CarbixEnergy/Carbix-Energy-Monitor/Docs/pics/readmepic.jpg

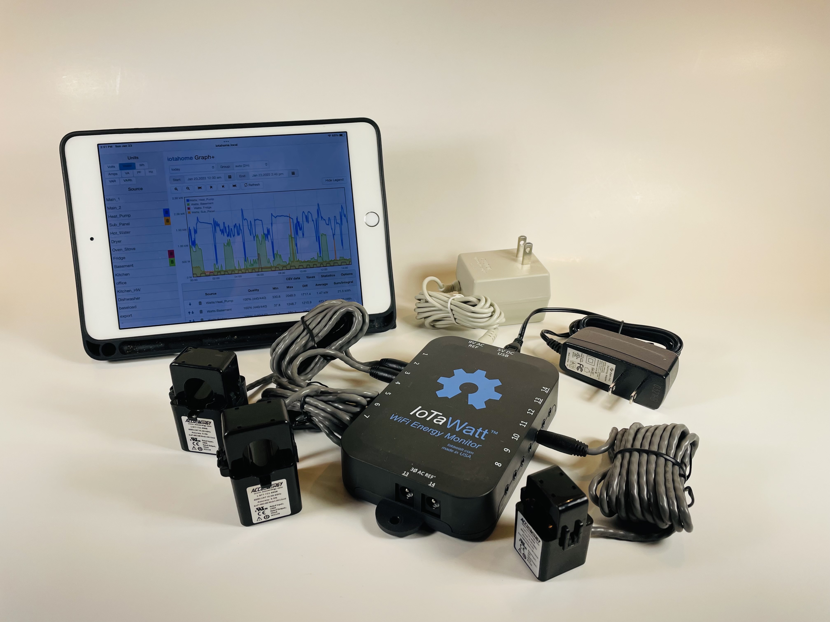
Docs/pics/readmepic.jpg
