CarbixEnergy/Carbix-Energy-Monitor/Docs/pics/USAbundle.jpg

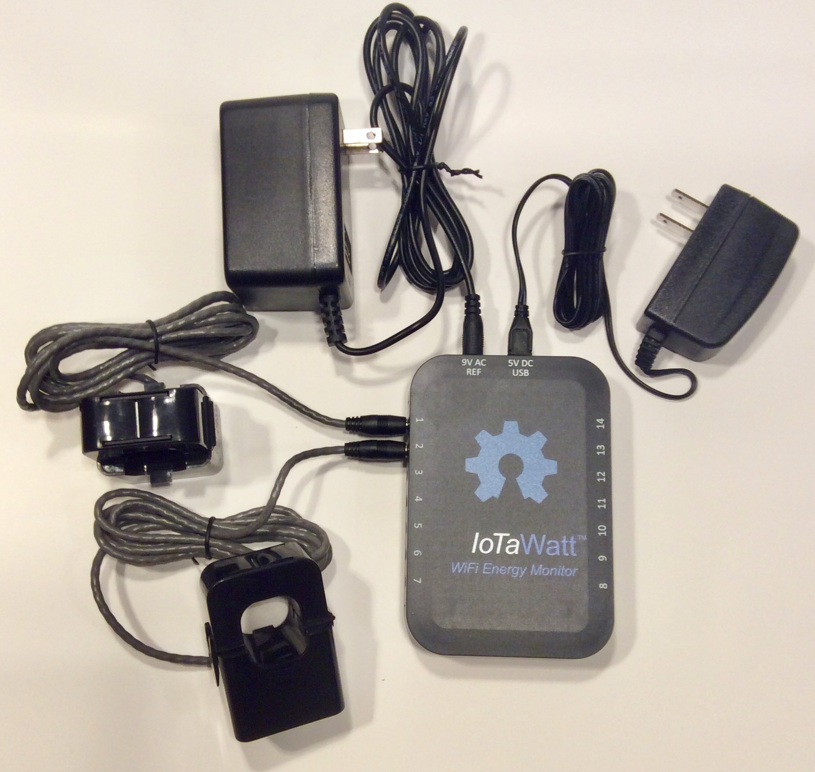
Docs/pics/USAbundle.jpg
