CarbixEnergy/Carbix-Energy-Monitor/Firmware/CarbixEnergyMonitor/updater.cpp

#include "CarbixEnergyMonitor.h"

bool   unpackUpdate(String updateVersion);

static const char updateURL_P[] PROGMEM = CARBIX_UPDATE_HOST;
static const char updatePath_P[] = CARBIX_VERSIONS_PATH;

/*************************************************************************************************
 * 
 *          updater - Service to check and update firmware
 * 
 *************************************************************************************************/
uint32_t updater(struct serviceBlock* _serviceBlock) {
  enum states {initialize, checkAutoUpdate, getVersion, waitVersion, createFile, download, waitDownload, install, getTable, waitTable};
  static states state = initialize;
  static asyncHTTPrequest* request = nullptr;
  static String updateVersion;
  static File releaseFile;
  static bool upToDate = false;
  static bool parseError = false;
  static int checkResponse = 0;
  static char* _updateClass = nullptr;
  static uint32_t lastVersionCheck = 0;
  static long latestTableVersion = -1;
  static uint32_t HTTPtoken = 0;

  trace(T_UPDATE,0); 
  if( ! WiFi.isConnected()){
    return UTCtime() + 1;
  }

  switch(state){

    case initialize: {
      trace(T_UPDATE,1);
      if( ! updateClass){
        updateClass = charstar("NONE");
      } 
      log("Updater: service started. Auto-update class is %s", updateClass);
      _updateClass = charstar(updateClass);
      tableVersion = getTablesVersion();
      state = checkAutoUpdate;
      return 1;
    }

    case checkAutoUpdate: {
      trace(T_UPDATE,2); 
      if( ! updateClass){
        updateClass = charstar("NONE");
      }
      if(strcmp(updateClass, _updateClass) != 0){
        delete[] _updateClass;
        _updateClass = charstar(updateClass);
        log("Updater: Auto-update class changed to %s", _updateClass);
        if (strcmp(updateClass, "NONE") != 0){
          lastVersionCheck = 0;
          upToDate = false;
          state = getVersion;
          return 1;
        }
      }
      else if (strcmp(_updateClass, "NONE") != 0 && UTCtime() - lastVersionCheck > updaterServiceInterval){
        lastVersionCheck = UTCtime();
        state = getVersion;
        return 1;
      }
      return UTCtime() + 7;
    }

    case getVersion: {
      trace(T_UPDATE,3); 
      if( ! WiFi.isConnected()){
        return UTCtime() + 1;
      }
      HTTPtoken = HTTPreserve(T_UPDATE);
      if( ! HTTPtoken){
        return UTCtime() + 1;
      }
      if( ! request){
        request = new asyncHTTPrequest;
      }
      request->setDebug(false);
      String URL(FPSTR(updateURL_P));
      URL += FPSTR(updatePath_P);
      if( ! request->open("GET", URL.c_str())){
        HTTPrelease(HTTPtoken);
        return UTCtime() + 60;
      }
      request->setTimeout(10);
      if( ! request->send()){
        request->abort();
        HTTPrelease(HTTPtoken);;
        return UTCtime() + 60;
      }
      state = waitVersion;
      return 1;
    }

    case waitVersion: {
      trace(T_UPDATE,4); 
      if(request->readyState() != 4){
        return UTCtime() + 1;
      }
      HTTPrelease(HTTPtoken);
      int responseCode = request->responseHTTPcode();
      String responseText = request->responseText();
      delete request;
      request = nullptr;

          // Handle error response

      if(responseCode != 200){
        if( responseCode != checkResponse){
          log("Updater: Invalid response from server. HTTPcode: %d", responseCode);
        }
        checkResponse = responseCode;
        state = checkAutoUpdate;
        if(responseCode == 403){
          lastVersionCheck = UTCtime();
        }
        return UTCtime() + 301;
      }
      DynamicJsonBuffer Json;
      JsonObject& response = Json.parseObject(responseText);
      if( ! response.success()){
        if(!parseError){
          log("Updater: could not parse versions.json file.");
        }
        parseError = true;
        state = checkAutoUpdate;
        lastVersionCheck = UTCtime();
        return 1;
      }
      parseError = false;

      // Check for "classes" object

      JsonObject& classes = response[F("classes")];
      if( ! classes.success()){
        if(!parseError){
          log("Updater: versions.json is invalid.");
        }
        parseError = true;
        state = checkAutoUpdate;
        lastVersionCheck = UTCtime();
        return 1;
      }      

            // Check if response contains the configured auto-update class

      if(classes.containsKey(updateClass)){
        updateVersion = classes[updateClass].as<char*>();
        if(updateVersion.equals(CARBIX_ENERGY_MONITOR_VERSION)){
          if( ! upToDate){
            log("Updater: Auto-update is current for class %s.", updateClass);
            upToDate = true;
          }
        }
        else {
          log("Updater: Update from %s to %s", CARBIX_ENERGY_MONITOR_VERSION, updateVersion.c_str());
          state = createFile;
          return 1;
        }
      }
      else {
        log("Updater: Unrecognized auto-update class %s.", updateClass);
        upToDate = true;
      }

            // Check tables file version

      if(response.containsKey(F("tables"))){
        latestTableVersion = parseSemanticVersion(response[F("tables")].as<char *>());
        if (latestTableVersion > tableVersion){
          log("Updater: update tables from %s to %s", displaySemanticVersion(tableVersion).c_str(), displaySemanticVersion(latestTableVersion).c_str());
          state = getTable;
          return 1;
        }
      }

      state = checkAutoUpdate;
      lastVersionCheck = UTCtime();
      return 1;
    }

    case createFile: {
      trace(T_UPDATE,5); 
      log("Updater: download %s", updateVersion.c_str());
      String filePath = "download/" + updateVersion + ".bin";
      deleteRecursive(filePath);
      releaseFile = SD.open(filePath.c_str(), FILE_WRITE);
      if(! releaseFile){
        log("Updater: Cannot create download file.");
        state = checkAutoUpdate;
        return UTCtime() + 60;
      }
      state = download;
      return 1;
    }
      
    case download: {
      trace(T_UPDATE,6);   
      if( ! WiFi.isConnected()){
        return UTCtime() + 1;
      }
      HTTPtoken = HTTPreserve(T_UPDATE, true);
      if( ! HTTPtoken){
        return UTCtime() + 1;
      }
      if( ! request){
        request = new asyncHTTPrequest;
      }
      String URL = String(FPSTR(updateURL_P)) + String(F(CARBIX_VERSIONS_DIR)) + updateVersion + ".bin";
      request->setDebug(false);
      trace(T_UPDATE,6);   
      if( ! request->open("GET", URL.c_str())){
        log("Updater: Cannot GET %s.", URL.c_str());
        HTTPrelease(HTTPtoken);
        state = checkAutoUpdate;
        lastVersionCheck = UTCtime();
        return 1;
      }
      trace(T_UPDATE,6);   
      request->setTimeout(5);
      request->onData([](void* arg, asyncHTTPrequest* request, size_t available){
        uint8_t *buf = new uint8_t[500];
        while(request->available()){
          size_t read = request->responseRead(buf, 500);
          releaseFile.write(buf, read);
        }
        delete[] buf;
        });
      request->send();

          // Writing to the SD in async handler can cause problems. If we return
          // and keep sampling, the onData handler could interupt another service
          // in the middle of SDcard work.  So we will go synchronous here and wait
          // for the entire update blob to be transfered and written to SD.
          // Takes about 5-10 seconds.

      setLedCycle(LED_UPDATING);
      while(request->readyState() != 4){
        yield();
      }
      trace(T_UPDATE,6);   
      endLedCycle();
      HTTPrelease(HTTPtoken);
      size_t fileSize = releaseFile.size();
      releaseFile.close();
      trace(T_UPDATE,6);   
      if(request->responseHTTPcode() != 200){
        log("Updater: Download failed HTTPcode %d", request->responseHTTPcode());
        delete request;
        request = nullptr;
        String filePath = "download/" + updateVersion + ".bin";
        deleteRecursive(filePath);
        state = checkAutoUpdate;
        lastVersionCheck = UTCtime();
        return 1;
      }
      log("Updater: Release downloaded %dms, size %d", request->elapsedTime(), fileSize);
      releaseFile.close();
      delete request;
      request = nullptr;
      state = install;
      return 1;
    }

    case install: {
      trace(T_UPDATE,7); 
      if(unpackUpdate(updateVersion)){
        if(installUpdate(updateVersion)){
          log ("Updater: Firmware updated, restarting.");
          delay(500);
          ESP.restart();
        }
      }
      state = checkAutoUpdate;
    }

    case getTable: {
      trace(T_UPDATE,10); 
      if( ! WiFi.isConnected()){
        return UTCtime() + 1;
      }
      HTTPtoken = HTTPreserve(T_UPDATE);
      if( ! HTTPtoken){
        return 250;
      }
      if( ! request){
        request = new asyncHTTPrequest;
      }
      String URL(FPSTR(CARBIX_UPDATE_HOST));
      URL += F(CARBIX_TABLE_DIR);
      URL += displaySemanticVersion(latestTableVersion);
      URL += ".txt";
      request->setDebug(false);
      if( ! request->open("GET", URL.c_str())){
        HTTPrelease(HTTPtoken);
        return UTCtime() + 60;
      }
      request->setTimeout(10);
      if( ! request->send()){
        request->abort();
        HTTPrelease(HTTPtoken);;
        return UTCtime() + 60;
      }
      state = waitTable;
      return 1;
    }

    case waitTable: {
      trace(T_UPDATE,20); 
      if(request->readyState() != 4){
        return 250;
      }
      HTTPrelease(HTTPtoken);
      int responseCode = request->responseHTTPcode();

          // Handle response

      if(responseCode == 200){
        if(SD.exists(F(CARBIX_NEW_TABLE_PATH))) SD.remove(F(CARBIX_NEW_TABLE_PATH));
        File tableFile = SD.open(F(CARBIX_NEW_TABLE_PATH), FILE_WRITE);
        if(!tableFile){
          return false;
        }
        uint8_t buf[512];
        while(request->available()){
          int len = request->responseRead(buf, 512);
          tableFile.write(buf, len);
        }
        tableFile.close();
        SD.remove(F(CARBIX_TABLE_PATH));
        SDFS.rename(F(CARBIX_NEW_TABLE_PATH), F(CARBIX_TABLE_PATH));
        tableVersion = getTablesVersion();
      }
      delete request;
      request = nullptr;
      lastVersionCheck = UTCtime();
      state = checkAutoUpdate;
      return 100;
    }
  }
  return UTCtime() + 1;
}

/**************************************************************************************************
 * bool unpackUpdate(String version)
 * 
 * unpack the release blob to create a directory of support files to be
 * installed during the next restart, as well as the firmware binary
 * file with md-5 appendage to be installed before restart.
 * 
 * After unpacking, the signature on the file is verified using the CarbixEnergyMonitor public key.
 * Only release files from CarbixEnergyMonitor.com can be verified because the private-key is needed to
 * sign with the digital signature.
 * 
 *************************************************************************************************/

bool unpackUpdate(String version){

  union {
    struct {
      char file[4];
      uint32_t len;
      char name[24];
    } fileHeader;
    struct { 
      char CarbixEnergyMonitor[8];
      char release[8];
    } updtHeader;
    uint8_t header[32];
  } headers;

  bool binaryFound = false;
  SHA256 sha256;
  MD5Builder md5;

        // open the release file and setup to sha256

  String filePath = "download/" + version + ".bin";
  File releaseFile = SD.open((char*)filePath.c_str(), FILE_READ);
  if(! releaseFile){
    log("Updater: %s not found", filePath.c_str());
    return false;
  }
  int signatureSize = 64;
  uint32_t binarySize = releaseFile.size() - signatureSize;
  sha256.reset();

        // Read and verify the header

  if(true){
    releaseFile.read(headers.header,sizeof(headers.updtHeader));
    sha256.update(headers.header,sizeof(headers.updtHeader));
    binarySize -= sizeof(headers.updtHeader);
    if((memcmp(headers.updtHeader.CarbixEnergyMonitor, "CarbixEM", 8) != 0) ||
       (memcmp(headers.updtHeader.release, version.c_str(), 8) != 0)) {
      log("Updater: release file header invalid. %s %s",headers.updtHeader.CarbixEnergyMonitor,headers.updtHeader.release);
      releaseFile.close();
      return false;
    }
  }
        // Create the local update directory.

  deleteRecursive(String(version));
  if( ! SD.mkdir(version.c_str())){
    log("Updater: Cannot create update directory");
    releaseFile.close();
    return false;
  }
        // Read the update blob and create the various files.

  while(binarySize){
    releaseFile.read(headers.header,sizeof(headers.fileHeader));
    sha256.update(headers.header,sizeof(headers.fileHeader));
    binarySize -= sizeof(headers.fileHeader);
    if(memcmp(headers.fileHeader.file,"FILE",4) != 0) {
      log("Updater: Release file format error.");
      releaseFile.close();
      return false;
    }
    String filename = String(headers.fileHeader.name);
    bool carbixenergymonitorBin = filename.equalsIgnoreCase("carbix.bin");
    if(carbixenergymonitorBin){
      binaryFound = true;
      md5.begin();
    }
    String filePath = version + "/" + headers.fileHeader.name;
    uint32_t fileSize = headers.fileHeader.len;
    File outFile = SD.open((char*)filePath.c_str(), FILE_WRITE);
    if( ! outFile){
      log("Updater: unable to create file: %s", filePath.c_str());
      releaseFile.close();
      return false;
    }
    int buffSize = 512;
    uint8_t* buff = new uint8_t [buffSize];
    while(fileSize){
      int chunk = MIN(fileSize, buffSize);
      if(chunk % 8) chunk += 8 - chunk % 8;
      releaseFile.read(buff, chunk);
      sha256.update(buff, chunk);
      binarySize -= chunk;
      outFile.write(buff, MIN(fileSize, buffSize));
      if(carbixenergymonitorBin) md5.add(buff, MIN(fileSize, buffSize));
      fileSize -= MIN(fileSize, buffSize);
    }
    delete[] buff;
    if(carbixenergymonitorBin) {
      md5.calculate();
      uint8_t md5Char[32];
      md5.getChars((char*)md5Char);
      outFile.write(md5Char, 32);
    }
    outFile.close();
    if(fileSize){
      return false;
    } 
  }
        // verify the signature

  
  uint8_t signature[64];
  uint8_t sha[32];
  sha256.finalize(sha,32);
  if(releaseFile.available() != 64){
    log("Updater: Update rejected, no signature.");
    releaseFile.close();
    return false;
  }
  releaseFile.read(signature, 64);
  releaseFile.close();
  
  uint8_t* key = new uint8_t[32];
  memcpy_P(key, publicKey, 32);
  if(! Ed25519::verify(signature, key, sha, 32)){
    log("Updater: Signature does not verify.");
    delete[] key;
    return false;
  }
  delete[] key;
  log("Updater: signature verified");
  return binaryFound;
}

/***********************************************************************************************************
 * bool installUpdate(String version)
 * 
 * Install the update in the directory "version".
 * Directory contains the ESP8266 binary "carbixenergymonitor.bin" with an md5 hash appended.
 * After binary is successfully updated, the ESP is restarted.
 * Upon restart, any files remaining in the update directory are 
 * placed in the SD root directory, replacing any pre-existing version.
 * 
 **********************************************************************************************************/

bool installUpdate(String version){
  UpdaterClass update;
  File inFile;
  String inPath = version + "/carbix.bin";
  inFile = SD.open((char*)inPath.c_str());
  if( ! inFile) return false;
  uint32_t inLen = inFile.size() - 32;
  update.begin(inLen);
  int buffSize = 512;
  uint8_t* buff = new uint8_t[buffSize];
  while(inLen){
    int chunk = MIN(inLen, buffSize);
    inFile.read(buff, chunk);
    update.write(buff, chunk);
    inLen -= chunk;
  }
  inFile.read(buff,32);
  update.setMD5((char*)buff);
  delete[] buff;
  if( ! update.end()){
    int error = update.getError();
    xbuf errorMsg;
    update.printError(errorMsg);
    log("Updater: %s", errorMsg.readStringUntil('\r').c_str());
    log("Updater: update failed");
    return false; 
  }
  SD.remove((char*)inPath.c_str());
  log("Updater: firmware upgraded to version %s", version.c_str());
  return true;
}

/************************************************************************************************************
 * bool copyUpdate(String version)
 * 
 * Copy release files staged in the update directory to the SD root.
 * Delete the files as they are copied and delete the directory when complete.
 * 
 ***********************************************************************************************************/

bool copyUpdate(String version){
  File updtDir = SD.open((char*)version.c_str());
  if( ! updtDir) return false;
  if( ! updtDir.isDirectory()){
    updtDir.close();
    SD.remove((char*)version.c_str());
    return false;
  }
  log("Updater: Installing update files for version %s", version.c_str());
  int buffSize = 512;
  uint8_t* buff = new uint8_t [buffSize];
  File inFile;
  while(inFile = updtDir.openNextFile()){
    if(strcmp_ci(inFile.name(),"config.txt") == 0 && SD.exists(inFile.name())){
      inFile.close();
      continue;
    }
    log("Updater: Installing %s", inFile.name());
    SD.remove(inFile.name());
    File outFile = SD.open(inFile.name(), FILE_WRITE);
    uint32_t fileSize = inFile.size();
    while(fileSize){
      int chunk = MIN(fileSize, buffSize);
      inFile.read(buff, chunk);
      outFile.write(buff, chunk);
      fileSize -= chunk;
    }
    inFile.close();
    outFile.close();
  }
  delete[] buff;
  log("Updater: Installation complete.");
  deleteRecursive(version);
  return true;
}

void printHex(uint8_t* data, size_t len){
  const char* hexchars = "0123456789abcdef";
  for(int i=0; i<len; i+=16){
    for(int j=i; j<(i+16); j++){
      if(j < len){
        Serial.print(hexchars[*data >> 4]);
        Serial.print(hexchars[*data++ & 0x0f]);
      }
      if((j % 4) == 3) Serial.print(" ");
    }
    Serial.println();
  }
}

long getTablesVersion(){
  File tableFile;
  tableFile = SD.open(F(CARBIX_TABLE_PATH), FILE_READ);
  if(!tableFile){
    return -1;
  }
  DynamicJsonBuffer Json;
  String tableSummary = JsonSummary(tableFile, 1);
  JsonObject& table = Json.parseObject(tableSummary);
  tableFile.close();

  if (!table.success()) {
    log("Table file parse failed.");
    return -1;
  }
  JsonObject &version = table[F("version")];
  if(table.containsKey(F("version"))){
    return parseSemanticVersion(table[F("version")].as<char*>());
  }
  return -1;
}
