CarbixEnergy/Carbix-Energy-Monitor/Firmware/CarbixEnergyMonitor/CSVquery.cpp

#include "CarbixEnergyMonitor.h"

CSVquery::CSVquery()
    :_oldRec(nullptr)
    ,_newRec(nullptr)
    ,_begin(0)
    ,_end(0)
    ,_limit(1000)
    ,_format(formatJson)
    ,_query(none)
    ,_header(false)
    ,_highRes(false)
    ,_integrations(false)
    ,_firstLine(true)
    ,_lastLine(false)
    ,_missingSkip(false)
    ,_missingNull(true)
    ,_missingZero(false)
    ,_timeOnly(false)
    ,_columns(nullptr)
    {}

CSVquery::~CSVquery(){
    trace(T_CSVquery,1,0);
    delete _oldRec;
    delete _newRec;
    trace(T_CSVquery,1,2);
    delete _columns;
    trace(T_CSVquery,1,3);
}

bool    CSVquery::setup(){
    trace(T_CSVquery,10);

                // query - show=series

    if(server.hasArg(F("show"))){
        String arg = server.arg(F("show"));
        if(arg.equalsIgnoreCase("series")){
           _format = formatJson;
           _query = show;
            return true; 
        }
        return false;
    }

                // query - select=[  ] 

    else if (server.hasArg(F("select"))){
    
        if( ! (server.hasArg(F("begin")) && server.hasArg(F("end")) && server.hasArg(F("group")) )){
            _failReason = F("Missing begin, end or group.");
            return false;
        }
       
        _begin = parseTimeArg(server.arg(F("begin")));
        if(_begin % Current_log.interval()){
            _begin += Current_log.interval() - (_begin % Current_log.interval());
        }
        _end = parseTimeArg(server.arg(F("end")));
        if(_end % Current_log.interval()){
            _end -= _end % Current_log.interval();
        }
        if(_end == 0 || _begin == 0 || _end < _begin) return false;
        trace(T_CSVquery,10);

        if(server.hasArg(F("resolution"))){
            String arg = server.arg(F("resolution"));
            if(arg.equalsIgnoreCase("low")){
                _highRes = false;
            }
            else if(arg.equalsIgnoreCase("high")){
                _highRes = true;
            }
            else {
                _failReason = F("Invalid resolution");
                return false;
            }
        }

        trace(T_CSVquery,10);
        String group = server.arg(F("group"));
        if(group.equals("auto")){
            const uint16_t intervals[] = {5, 10, 15, 20, 30, 60, 120, 300, 600, 1200, 1800, 3600, 7200, 14400, 21600, 28800};
            uint32_t rawInterval = (_end - _begin) / (_highRes ? 800 : 400);
            uint32_t interval = 86400;
            for(int i=0; i<16; i++){
                if(rawInterval <= intervals[i]){
                    interval = intervals[i];
                    break; 
                }
            }
            _groupMult = interval;
            _groupUnits = tUnitsSeconds;
        } else if(group.equals("all")){
            _groupMult = _end - _begin;
            _groupUnits = tUnitsSeconds;
        } else {
            _groupMult = MAX(1, group.toInt());
            if(group.endsWith("s")) _groupUnits = tUnitsSeconds;
            else if(group.endsWith("m")) _groupUnits = tUnitsMinutes;
            else if(group.endsWith("h")) _groupUnits = tUnitsHours;
            else if(group.endsWith("d")) _groupUnits = tUnitsDays;
            else if(group.endsWith("w")) _groupUnits = tUnitsWeeks;
            else if(group.endsWith("M")) _groupUnits = tUnitsMonths;
            else if(group.endsWith("y")) _groupUnits = tUnitsYears;
            else if(_groupMult > 0 && _groupMult % 5 == 0) _groupUnits = tUnitsSeconds;
            else {
                _failReason = F("Invalid group");
                return false;
            }
        }
        if((_begin % 60 == 0) && (_end % 60 == 0) && (_groupUnits != tUnitsSeconds || _groupMult % 60 == 0)){
            _integrations = true;
        }
        else if(_groupUnits == tUnitsSeconds && _begin >= Current_log.firstKey()){
            _integrations = true;
        }

        if(server.hasArg(F("missing"))){
            String arg = server.arg(F("missing"));
            _missingSkip = (arg.equalsIgnoreCase("skip")) ? true : false;
            _missingNull = (arg.equalsIgnoreCase("null")) ? true : false;
            _missingZero = (arg.equalsIgnoreCase("zero")) ? true : false;
        }
        if(server.hasArg(F("header"))){
            String arg = server.arg(F("header"));
            if(arg.equalsIgnoreCase("yes")) _header = true;
            if(arg.equalsIgnoreCase("no")) _header = false;
        }
        if(server.hasArg(F("format"))){
            String arg = server.arg(F("format"));
            if(arg.equalsIgnoreCase("json")){
                _format = formatJson;
            }
            else if(arg.equalsIgnoreCase("CSV")){
                _format = formatCSV;
            }
            else {
                _failReason = F("Invalid format");
                return false;
            }
        }

        if(server.hasArg(F("limit"))){
            String arg = server.arg(F("limit"));
            if (arg.equalsIgnoreCase("none")) {
                _limit = -1;
            }
            else {
                _limit = arg.toInt();
                if(_limit == 0){
                    _failReason = F("Invalid limit");
                    return false;
                }
            }
        }
        
        trace(T_CSVquery,10);

            // Parse the columns array and build list of column table entries.

        trace(T_CSVquery,12);
        String array = server.arg(F("select"));
        if( ! (array.startsWith("[") && array.endsWith("]"))){
            _failReason = F("select not an array []");
            return false;
        }
        array = array.substring(1,array.length()-1);

        String header;
        trace(T_CSVquery,13);
        while(array.length()){

                // Add a column to the list

            column* col = new column;
            col->next = _columns;
            _columns = col;
            
                // Parse the next element from the array

            trace(T_CSVquery,13);
            String element;
            int index = array.indexOf(',');
            if(index == -1){
                element = array;
                array = "";
            }
            else {
                element = array.substring(0,index);
                array.remove(0,index+1);
            }

                // Parse the name of the element
            
            trace(T_CSVquery,13);
            String name = element;
            int period = element.indexOf('.');
            if(period != -1){
                name.remove(period);
                element.remove(0,period+1);
                element.toLowerCase();
            } else {
                element = "";
            }
            if(name.length() == 0) continue;

            if(name.equalsIgnoreCase("time")){
                col->source = 'T';
                col->timeFormat = iso;
                col->timeLocal = true;
            }
            
            if(col->source == ' '){
                trace(T_CSVquery,14);
                for(int j=0; j<maxInputs; j++){
                    if(inputChannel[j]->isActive() && name.equals(inputChannel[j]->_name)){
                        col->source = 'I';
                        if(inputChannel[j]->_type == channelTypeVoltage){
                            col->unit = Volts;
                        } else {
                            col->unit = Watts;
                        }
                        col->input = inputChannel[j]->_channel;
                        break;
                    }
                }
            }

            if(col->source == ' '){
                trace(T_CSVquery,16);
                Script* script = outputs->first();
                while(script){
                    if(name.equals(script->name())){
                        col->source = 'O';
                        if(strcmp(script->getUnits(),"Volts") == 0){
                            col->unit = Volts;
                        }
                        else if(strcmp(script->getUnits(),"Watts") == 0){
                            col->unit = Watts;
                        }
                        else col->decimals = script->precision();
                        col->script = script;
                        break;
                    } 
                    script = script->next(); 
                }  
            }

            if(col->source == ' '){
                _failReason = String(F("Invalid series: ")) + name;
                return false;
            }

                // Process any methods

            while(element.length()){
                String method = element;
                period = element.indexOf('.');
                if(period != -1){
                    method.remove(period);
                    element.remove(0,period+1);
                } else {
                    element = "";
                }
                if(method.length() == 0) continue;

                if(col->source == 'T'){
                    if(method.equals("local")) col->timeLocal = true;
                    else if(method.equals("utc")) col->timeLocal = false;
                    else if(method.equals("iso")) col->timeFormat = iso;
                    else if(method.equals("unix")) col->timeFormat = unix;
                    else {
                        _failReason = String(F("invalid time method: ")) + method;
                        return false;
                    }
                }

                else if(method.equalsIgnoreCase("volts")){
                    col->unit = Volts;
                    col->decimals = 1;
                }
                else if(method.equalsIgnoreCase("watts")){
                    col->unit = Watts;
                    col->decimals = 1;
                }
                else if(method.equalsIgnoreCase("wh")){
                    col->unit = Wh;
                    col->decimals = 0;
                }
                else if(method.equalsIgnoreCase("amps")){
                    col->unit = Amps;
                    col->decimals = 1;
                }
                else if(method.equalsIgnoreCase("va")){
                    col->unit = VA;
                    col->decimals = 1;
                }
                else if(method.equalsIgnoreCase("hz")){
                    col->unit = Hz;
                    col->decimals = 2;
                }
                else if(method.equalsIgnoreCase("pf")){
                    col->unit = PF;
                    col->decimals = 1;
                }
                else if(method.equalsIgnoreCase("var")){
                    col->unit = VAR;
                    col->decimals = 1;
                }
                else if(method.equalsIgnoreCase("varh")){
                    col->unit = VARh;
                    col->decimals = 0;
                }
                else if(method.startsWith("d")){
                    if(method.length() != 2 | method[1] < '0' | method[1] > '9') return false;
                    col->decimals = method[1] - '0';
                }
                else {
                    _failReason = String(F("Invalid series method: ")) + method;
                    return false;
                }
            }
            trace(T_CSVquery,17);
        }

            // Convert list from LIFO to FIFO and create Scripts for inputs

        column* col = _columns;
        column* prev = nullptr;
        while(col){
            if(col->source == 'I'){
                int input = col->input;
                char newscript[4];
                snprintf(newscript,4,"@%d",input);
                col->script = new Script(inputChannel[input]->_name, unitstr(col->unit), newscript);
            }

            column* next = col->next;
            col->next = prev;
            prev = col;
            col = next;
        }
        _columns = prev;
        if(_columns->next == nullptr && _columns->source == 'T'){
            _timeOnly = true;
        }

        // Display the columns

        trace(T_CSVquery,18);
        col = _columns;
        while(col){
            String name;
            if(col->source == 'I'){
                name = inputChannel[col->input]->_name;
            }
            if(col->source == 'O'){
                name = col->script->name();
            }
            col = col->next;
        }

        trace(T_CSVquery,19);
        if(_header){
            buildHeader();
        }
        if(_format == formatJson){
            _buffer.print('[');
        }
        _oldRec = new CarbixLogRecord;
        _newRec = new CarbixLogRecord;
        _newRec->UNIXtime = _begin;
        logReadKey(_newRec);
        trace(T_CSVquery,20);
        _query = select;
        return true;
    }

    // unrecognized query (not show or select)

    else {
        return false;
    }
}

const char*  CSVquery::unitstr(units units){
    if(units == Volts) return "Volts";
    if(units == Watts) return "Watts";
    if(units == kWh)   return "kWh";
    if(units == Hz)    return "Hz";
    if(units == Amps)  return "Amps";
    if(units == VA)    return "VA";
    if(units == PF)    return "PF";
    if(units == VAR)   return "VAR";
    if(units == VARh)  return "VARh";
    return "Watts";

}
 
bool    CSVquery::isJson(){
    return _format == formatJson;
}
bool    CSVquery::isCSV(){
    return _format == formatCSV;
}

String  CSVquery::failReason(){
    return _failReason.length() ? _failReason : "unspecified";
}

//*****************************************************************************************
//                  buildHeader
//*****************************************************************************************
void CSVquery::buildHeader(){

    if(_format == formatJson){
        _buffer.printf_P(PSTR("{\"range\":[%d,%d],\"labels\":["), _begin, _end);
    }
    column* col = _columns;
    bool first = true;
    while(col){
        if( ! first){
            _buffer.print(',');
            if(_format == formatCSV){
                _buffer.print(' ');
            }
        } 
        first = false;
        if(_format == formatJson){
            _buffer.print('"');
        }
        if(col->source == 'T'){
            _buffer.print("Time");
        }
        else if (col->source == 'I'){
            _buffer.print(inputChannel[col->input]->_name);
        }
        else if(col->source == 'O'){
            _buffer.print(col->script->name());
        }
        else if(col->source == 'N'){
            _buffer.print(col->script->name());
        }
        if(_format == formatJson){
            _buffer.print('"');
        }
        col = col->next;
    }

    if(_format == formatJson){
        _buffer.print("],\r\n\"data\":");
    }
    else if(_format == formatCSV){
        _buffer.print("\r\n");
    }
    return;
}

//*****************************************************************************************
//                  buildLine
//*****************************************************************************************
void CSVquery::buildLine(){
    trace(T_CSVquery,60);
    column* col = _columns;
    double elapsedHours = _newRec->logHours - _oldRec->logHours;
    bool first = true;
        
    while(col){
        trace(T_CSVquery,61);

        if( ! first){
            if(_format == formatJson){
                _buffer.print(',');
            } else {
                _buffer.print(", ");
            }
        } 
        first = false;

        if(elapsedHours == 0 && _missingSkip){
            continue;
        }

        else if(col->source == 'T'){
            time_t Time = col->timeLocal ? UTC2Local(_oldRec->UNIXtime) : _oldRec->UNIXtime;
            if(col->timeFormat == unix){
                _buffer.print(Time);
            }
            else {
                trace(T_CSVquery,62);
                _tm = gmtime(&Time); 
                char out[80];
                strftime(out, 80, "%FT%T", _tm);
                if(_format == formatJson){
                    _buffer.printf("\"%s\"", out);    
                } else {
                    _buffer.print(out);
                }
            }
        }

        else if(elapsedHours == 0){
            trace(T_CSVquery,63);
            if(_missingZero){
                _buffer.print('0');
            }
            else if(_missingNull){
                _buffer.print("null");
            }
        }

        else {
            trace(T_CSVquery,64);
            double value = 0.0;
            value = col->script->run(_oldRec, _newRec, col->unit);
            trace(T_CSVquery,65);
            printValue(value, col->decimals);
        }

    col = col->next;
    }

}

void CSVquery::printValue(const double value, const int8_t decimals){
    char str[20];
    snprintf(str,20,"%#.*f",decimals,value);
    int len = strlen(str);
    while(str[--len] == '0');
    if(str[len] == '.') --len;
    str[len+1] = 0;
    _buffer.write(str);
}

//*****************************************************************************************
//                  readResult
//*****************************************************************************************
size_t  CSVquery::readResult(uint8_t* buf, int len){

    trace(T_CSVquery,20);
    switch (_query){

        default:
        case none: {
            return 0;
        }

        case show: {

            trace(T_CSVquery,30);
            if(!_lastLine){
                char leader = '[';
                _buffer.write("{\"series\":");

                for(int j=0; j<maxInputs; j++){
                    if(inputChannel[j]->isActive()){
                        String units;
                        if(inputChannel[j]->_type == channelTypeVoltage){
                            units = "Volts";
                        } else if(inputChannel[j]->_type == channelTypePower){
                            units = "Watts";
                        }
                        else continue;
                        _buffer.printf_P(PSTR("%c{\"name\":\"%s\",\"unit\":\"%s\"}"), leader, inputChannel[j]->_name, units.c_str());
                        leader = ',';
                    }
                }

                Script* script = outputs->first();
                while(script){
                    _buffer.printf_P(PSTR("%c{\"name\":\"%s\",\"unit\":\"%s\"}"), leader, script->name(), script->getUnits());
                    script = script->next(); 
                }  
                _buffer.write("]}");
                _lastLine = true;
            }

            int written = 0;
            if(_buffer.available()){
                int supply = _buffer.available();
                int demand = len - written;
                if(demand < supply){
                    supply = demand;
                }
                _buffer.read(buf+written, supply);
                written += supply;
            }
            trace(T_CSVquery,31);
            return written;
        }

        case select: {

                    // Loop to fill caller buf
                    // Order is important to avoid boundary conditions.

            trace(T_CSVquery,40);
            int written = 0;
            while(true){
                trace(T_CSVquery,41);

                    // Transfer _buffer to caller buffer

                if(_buffer.available()){
                    trace(T_CSVquery,42);
                    int supply = _buffer.available();
                    int demand = len - written;
                    if(demand < supply){
                        supply = demand;
                    }
                    _buffer.read(buf+written, supply);
                    written += supply;
                    if(written == len){
                        trace(T_CSVquery,43);
                        return written;
                    }
                }

                    // If ended, just return zero 
                
                else if(_lastLine){
                    trace(T_CSVquery,44);
                    return written;
                }

                    // If at end of range, or limit reached
                    // Finish output stream and break.

                else if(_newRec->UNIXtime >= _end || _limit == 0){
                    trace(T_CSVquery,45);
                    if(_format == formatJson){
                        _buffer.print(']');
                    }
                    if(_limit == 0 && _newRec->UNIXtime < _end){
                        if(_format == formatCSV){
                            _buffer.printf_P(PSTR("\r\nLimit exceeded at %d"), _newRec->UNIXtime);
                        }
                        else if(_header){
                            _buffer.printf_P(PSTR(",\"limit\":%d"), _newRec->UNIXtime);
                        }
                    }
                    if(_format == formatJson && _header){
                        _buffer.print('}');
                    }
                    _lastLine = true;
                }

                    // Process next group

                else {
                    trace(T_CSVquery,50);

                        // Age the log record
                    
                    CarbixLogRecord* swapRec = _oldRec;
                    _oldRec = _newRec;
                    _newRec = swapRec;

                        // Read group end record

                    _newRec->UNIXtime = (uint32_t)nextGroup((time_t)_oldRec->UNIXtime, _groupUnits, _groupMult);
                    if( ! _timeOnly){
                        trace(T_CSVquery,51);
                        logReadKey(_newRec);
                    }

                        // Belt and suspenders,
                        // Make sure we are moving forward.

                    if(_newRec->UNIXtime <= _oldRec->UNIXtime){
                        trace(T_CSVquery,52);
                        _lastLine = true;
                    }

                        // If there is data or not skipping missing data, 
                        // Generate a line.             

                    if( _timeOnly || (! (_newRec->logHours == _oldRec->logHours && _missingSkip))){
                        trace(T_CSVquery,53);    
                        if( ! _firstLine){
                            if(_format == formatJson){
                                _buffer.print(',');
                            }
                            if(_format == formatCSV){
                                _buffer.print("\r\n");
                            }
                        }

                        if(_format == formatJson){
                            _buffer.print('[');
                        }
                        trace(T_CSVquery,54);    
                        buildLine();
                        _limit--;
                        trace(T_CSVquery,55);

                        if(_format == formatJson){
                            trace(T_CSVquery,56);
                            _buffer.print(']');
                        }

                        _firstLine = false;
                    }
                }
            }
        }
    }
}

time_t  CSVquery::nextGroup(time_t time, tUnits units, int32_t inc){
    time_t result;

    if(units == tUnitsSeconds){
        result = time + inc;
    }
    else if(units == tUnitsMinutes){
        result = time + (60 * inc) - (time % 60);
    }
    else if(units == tUnitsHours){
        result = time + (3600 * inc) - (time % 3600);
    }
    else {
        time_t local = localTime((uint32_t) time); 
        _tm = gmtime(&local);
        _tm->tm_hour = _tm->tm_min = _tm->tm_sec = 0;
        if(units == tUnitsDays){
            _tm->tm_mday += inc;
        } 
        else if(units == tUnitsWeeks){
            _tm->tm_mday += (7 * inc) - (_tm->tm_wday);
        } 
        else if(units == tUnitsMonths){
            _tm->tm_mon += inc;
            _tm->tm_mday = 1; 
        } 
        else if(units == tUnitsYears){
            _tm->tm_year += inc;
            _tm->tm_mon = 0;
            _tm->tm_mday = 1; 
        }
        result = UTCtime((uint32_t) mktime(_tm));
    }
    return (time_t)MIN(_end, result);
}

//*****************************************************************************************
//
//      parseTimeArg - parse and interpret time argument
//
//      Can be:
//  
//      UNIX time value in seconds (10 char) or ms (13 char).  Interpreted as local time
//
//      Date/time as YYYY [-MM [-DD [THH [:MM [:SS [Z]]]]]]
//                   Interpreted as local time unless ends with "Z"
//      
//      Relative local time expression:
//          base time [modifier [modifier....]]
//          base time is start of current:  y   year
//                                          M   month
//                                          w   week
//                                          d   day
//                                          h   hour
//                                          m   minute
//                                          s   last 5 seconds (equivalent to "now")
//
//          modifiers are:  +/- N period where:
//                                          y   years
//                                          M  months   
//                                          w   weeks
//                                          d   days
//                                          h   hours
//                                          m   minutes
//                                          s   seconds (N is mult of 5)    
//
//          examples period begin and end:
//          
//                                      begin       end
//          today                       d           s
//          last hour                   s-1h        s
//          last 12 hours               s-12h       s
//          yesterday                   d-1d        d
//          month to date               M           s
//          past two weeks              w-2w        w
//          last 6 whole months         M-6M        M
//          last 6 months               s-6m        s
//          last day of last month      M-1d        M
//
//          This method can be very powerful and honors DST.  It is also independent of
//          browser time zone, using the CarbixEnergyMonitor time zone.
//
//*****************************************************************************************
time_t  CSVquery::parseTimeArg(String timeArg){
    time_t local = localTime();
    char arg[32];
    strncpy(arg, timeArg.c_str(), 31);
    arg[31] = 0;
    char* ptr = arg;

        // Check for UNIXtime. 

    uint32_t unixtime = 0;
    int digits = 0;
    while(*ptr >= '0' && *ptr <= '9'){
        if(++digits <= 10){
            unixtime = (unixtime * 10) + (*ptr - '0');
        }
        ptr++;
    }
    if(*ptr == 0 && (digits == 10 || digits == 13)) return unixtime;
    
        // Check for date

    ptr = arg;
     
    int year = parseInt(&ptr);
    if(year >= 2000 && year <= 2099){
        time_t JAN_1_2000 = 946684800UL; 
        _tm = gmtime(&JAN_1_2000);
        _tm->tm_year = year - 1900;
        if(*(ptr++) == '-'){
            _tm->tm_mon = parseInt(&ptr);
            if(_tm->tm_mon >= 1 && _tm->tm_mon <=12 && *(ptr++) == '-'){
                _tm->tm_mon--;
                _tm->tm_mday = parseInt(&ptr);
                if(_tm->tm_mday >= 1 && _tm->tm_mday <=31 && *(ptr++) == 'T'){
                    _tm->tm_hour = parseInt(&ptr);
                    if(_tm->tm_hour >= 0 && _tm->tm_hour <=24 && *(ptr++) == ':'){
                        _tm->tm_min = parseInt(&ptr);
                        if(_tm->tm_min >= 0 && _tm->tm_min <= 59 && *(ptr++) == ':'){
                            _tm->tm_sec = parseInt(&ptr);
                            ptr++;
                        }
                    }
                }
            }
        }
        ptr--;
        if(*ptr == 0){
            return UTCtime((uint32_t) mktime(_tm));
        }
        else if(*ptr == 'Z' && *(ptr+1) == 0){
            return mktime(_tm);
        }
        else return 0;
    }

        // Check for starting identifier

    ptr = arg;
    _tm = gmtime(&local);
    _tm->tm_sec -= _tm->tm_sec % 5;
    switch (*ptr){
        default: return 0;
        case 'y': _tm->tm_mon = 0;
        case 'M': _tm->tm_mday = 1;
        case 'd': _tm->tm_hour = 0;
        case 'h': _tm->tm_min = 0;
        case 'm': _tm->tm_sec = 0;
                  break;
        case 's': break;
        case 'w': _tm->tm_mday -= _tm->tm_wday;
                  _tm->tm_hour = 0;
                  _tm->tm_min = 0;
                  _tm->tm_sec = 0;
                  break;
    }
    ptr++;
    
        // Process any modifiers

    while(*ptr != 0){
        if(*ptr != '-' && *ptr != '+') return 0;
        long mult = strtol(ptr, &ptr, 10);
        if(mult == 0) return 0;
        switch (*ptr){
            default: return 0;
            case 'y': _tm->tm_year += mult; break;
            case 'M': _tm->tm_mon += mult; break;
            case 'w': _tm->tm_mday += 7 * mult; break;
            case 'd': _tm->tm_mday += mult; break;
            case 'h': _tm->tm_hour += mult; break;
            case 'm': _tm->tm_min += mult; break;
            case 's': _tm->tm_sec += mult - (mult % 5); break;
        }
        ptr++;
    }
    return UTCtime((uint32_t) mktime(_tm));
}

int    CSVquery::parseInt(char** ptr){
    return strtoul(*ptr, ptr, 10);
}
