CarbixEnergy/Carbix-Energy-Monitor/Firmware/CarbixEnergyMonitor/GetFeedData.cpp

#include "CarbixEnergyMonitor.h"

/***************************************************************************************************
 *  GetFeedData SERVICE.
 *  
 *  The web server does a pretty good job of handling file downloads and uploads asynchronously, 
 *  but assumes that any callbacks to new handlers get the job completely done befor returning. 
 *  The GET /feed/data/ request takes a long time and generates a lot of data so it needs to 
 *  run as a SERVICE so that sampling can continue while it works on providing the data.  
 *  To accomplish that without modifying ESP8266WebServer, we schedule this SERVICE and
 *  block subsequent calls to server.handleClient() until the request is satisfied, at which time
 *  this SERVICE returns with code 0 to cause it's serviceBlock to be deleted.  When a new /feed/data
 *  request comes in, the web server handler will reshedule this SERVICE with NewService.
 * 
 *  The process time per dispatch is determined to try to balance sampling with response time.
 *  When a new request is soon after another, the process time is decreased to maintain
 *  sampling at the expense of response time.
 * 
 *  ********NOTE*******
 *  7/22/2018 Made this a direct call from webserver so entire transaction is handled without
 *  returning to allow sampling. This seems to eliminate memory leak problems with sending the
 *  response data after essentially ending the transaction by returning from the initial webserver call.
 *  Improves query response times, but stops sampling for about 1.3-1.5sec for a typical graph request.
 * 
 *  Stopping sampling doesn't mean power is not logged.  It only means that changes to power
 *  during that period will not be measured. 
 * 
 *  Other solutions that can be explored in the future might be:
 * 
 *  1) sample power directly from within the webserver handler (ugh).
 *  2) determine what is not being cleaned up and find a way to do so. Suspect it's 
 *     request headers as the problem is more severe when digest auth headers are collected.
 *  3) Try using asyncwebserver.
 *   
 **************************************************************************************************/

uint32_t getFeedData(){ //(struct serviceBlock* _serviceBlock){
  // trace T_GFD

  struct req {
    req* next;
    int channel;
    char queryType;
    Script* output;
    req(){next=nullptr; channel=0; queryType=' '; output=nullptr;};
    ~req(){delete next;};
  }; 

  static CarbixLogRecord* logRecord = nullptr;
  static CarbixLogRecord* lastRecord = nullptr;
  static size_t   chunkSize = 1600;
  static char* buf = nullptr;
  static size_t bufPos = 0;
  static String*  replyData = nullptr;
  static req*     reqRoot = nullptr;
  static uint32_t startUnixTime;
  static uint32_t endUnixTime;
  static uint32_t intervalSeconds;
  static uint32_t UnixTime;
  static uint32_t lastReqTime = 0;
  static uint32_t processInterval;
  static uint32_t startTime;
  static bool     modeRequest;
  enum   states   {setup, process} static state = setup;
       
  switch (state) {
    
    case setup: {
      trace(T_GFD,0);
      startTime = millis();
      processInterval = 3000 / (uint32_t)(frequency + 0.1);
      if((millis() - lastReqTime) > 10000){
        processInterval = 6000 / (uint32_t)(frequency + 0.1);
      }
      lastReqTime = millis();

        // Validate the request parameters
      
      startUnixTime = server.arg("start").substring(0,10).toInt();
      endUnixTime = server.arg("end").substring(0,10).toInt();
      if(server.hasArg("interval")){
        intervalSeconds = server.arg("interval").toInt();
        modeRequest = false;;
      }
      else if(server.hasArg("mode")){
        modeRequest = true;
        if(server.arg("mode")== "daily") intervalSeconds = 86400;
        else if(server.arg("mode") == "weekly") intervalSeconds = 86400 * 7;
        else if(server.arg("mode") == "monthly") intervalSeconds = 86400 * 30;
        else if(server.arg("mode") == "yearly") intervalSeconds = 86400 * 365;
      }
      if((startUnixTime % 5) ||
         (endUnixTime % 5) ||
         (intervalSeconds % 5) ||
         (intervalSeconds <= 0) ||
         (endUnixTime < startUnixTime) ||
         ((endUnixTime - startUnixTime) / intervalSeconds > 2000)) {
        server.send(400, "text/plain", "Invalid request");
        state = setup;
        serverAvailable = true;
        return 0;    
      }
      
          // Parse the ID parm into a list.
      
      String idParm = server.arg("id");
      if( ! reqRoot) reqRoot = new req;
      req* reqPtr = reqRoot;
      int i = 0;
      if(idParm.startsWith("[")){
        idParm[idParm.length()-1] = ',';
        i = 1;
      } else {
        idParm += ",";
      }
      while(i < idParm.length()){
        reqPtr->next = new req;
        reqPtr = reqPtr->next;
        String id = idParm.substring(i,idParm.indexOf(',',i));
        String name = id.substring(2);
        i = idParm.indexOf(',',i) + 1;
        if(id.charAt(0) == 'I'){
          for(int j=0; j<maxInputs; j++){
            if(inputChannel[j]->isActive() &&
               name.equals(inputChannel[j]->_name)){
               reqPtr->channel = inputChannel[j]->_channel;
               reqPtr->output = nullptr;
               reqPtr->queryType = id.charAt(1);
               break;
            }
          }
        }
        else if(id.charAt(0) == 'O'){
          Script* script = outputs->first();
          while(script){
            if(name.equals(script->name())){
              reqPtr->channel = -1;
              reqPtr->output = script;
              reqPtr->queryType = id.charAt(1);
              break;
            } 
            script = script->next(); 
          }  
        }
      }
          
      logRecord = new CarbixLogRecord;
      lastRecord = new CarbixLogRecord;
     
      if(startUnixTime >= History_log.firstKey()){   
        lastRecord->UNIXtime = startUnixTime - intervalSeconds;
      } else {
        lastRecord->UNIXtime = History_log.firstKey();
      }
      logReadKey(lastRecord);
      
          // Using String for a large buffer abuses the heap
          // and takes up a lot of time. We will build 
          // relatively short response elements with String
          // and copy them to this larger buffer.

      buf = new char[chunkSize+8];
      bufPos = 6;
      replyData = new String();
      
          // Setup buffer to do it "chunky-style"
      
      server.setContentLength(CONTENT_LENGTH_UNKNOWN);
      server.send(200,"application/octet-stream","");
      *replyData= "[";
      UnixTime = startUnixTime;
      state = process;
    }
  
    case process: {
      trace(T_GFD,1);

          // Loop to generate entries
      
      while(UnixTime <= endUnixTime) {
        int rtc;
        logRecord->UNIXtime = UnixTime;
        logReadKey(logRecord);
        trace(T_GFD,2);
        *replyData += '[';  //  + String(UnixTime) + "000,";
        double elapsedHours = logRecord->logHours - lastRecord->logHours;
        req* reqPtr = reqRoot;
        while((reqPtr = reqPtr->next) != nullptr){
          int channel = reqPtr->channel;
          if(rtc || logRecord->logHours == lastRecord->logHours){
            *replyData +=  "null";
          }
  
            // input channel

          else if(channel >= 0){
            trace(T_GFD,3);       
            if(reqPtr->queryType == 'V') {
              *replyData += String((logRecord->accum1[channel] - lastRecord->accum1[channel]) / elapsedHours,1);
            } 
            else if(reqPtr->queryType == 'P') {
              *replyData += String((logRecord->accum1[channel] - lastRecord->accum1[channel]) / elapsedHours,1);
            }
            else if(reqPtr->queryType == 'E') {
                *replyData += String((logRecord->accum1[channel] / 1000.0),3);              
            } 
            else {
              *replyData += "null";
            } 
          }
  
           // output channel
          
          else {
            trace(T_GFD,4);
            if(reqPtr->output == nullptr){
              *replyData += "null";
            }
            else if(reqPtr->queryType == 'V'){
              *replyData += String(reqPtr->output->run(lastRecord, logRecord, Volts), 1);
            }
            else if(reqPtr->queryType == 'P'){
              *replyData += String(reqPtr->output->run(lastRecord, logRecord, Watts), 1);
            }
            else if(reqPtr->queryType == 'E'){
                *replyData += String(reqPtr->output->run(nullptr, logRecord, kWh), 3);
            }
            else if(reqPtr->queryType == 'O'){
              *replyData += String(reqPtr->output->run(lastRecord, logRecord), reqPtr->output->precision());
            }
            else {
              *replyData += "null";
            }
          }
          if(replyData->endsWith("NaN") || replyData->endsWith("inf")){
            replyData->remove(replyData->length()-3);
            *replyData += "null";
          }
          *replyData += ',';
        } 
           
        replyData->setCharAt(replyData->length()-1,']');
        CarbixLogRecord* swapRecord = lastRecord;
        lastRecord = logRecord;
        logRecord = swapRecord;
        UnixTime += intervalSeconds;

            // If not enough room in buffer for this segment, 
            // Write the buffer chunk.

        if((bufPos + replyData->length()) > (chunkSize - 3)){
          sendChunk(buf, bufPos);
          bufPos = 6;
        }    

            // Add this segment to buf.

        trace(T_GFD,5);
        memcpy(buf + bufPos, replyData->c_str(), replyData->length());
        bufPos += replyData->length();
        replyData->remove(0);
        
        *replyData += ',';
      }
      trace(T_GFD,7);

          // All entries generated, terminate Json and send.
      
      replyData->setCharAt(replyData->length()-1,']');
      memcpy(buf + bufPos, replyData->c_str(), replyData->length());
      bufPos += replyData->length();
      sendChunk(buf, bufPos);

      delete replyData;
      replyData = nullptr;
      
          // Send terminating zero chunk, clean up and exit.    
      
      sendChunk(buf, 6);
      server.client().stop();
      trace(T_GFD,7);
      delete[] buf;
      buf = nullptr;
      delete reqRoot;
      reqRoot = nullptr;
      delete logRecord;
      logRecord = nullptr;
      delete lastRecord;
      lastRecord = nullptr;
      state = setup;
      serverAvailable = true;
      return 0;                                       // Done for now, return without scheduling.
    }
  }
  return 0;
}
