CarbixEnergy/Carbix-Energy-Monitor/Firmware/CarbixEnergyMonitor/dataLog.cpp

 /**********************************************************************************************
 * dataLog is a SERVICE that posts the raw input data from the "buckets" to a file on the SDcard.
 * The CarbixLog class handles the SD file work.
 * If there is no file, it will be created.
 * 
 * The log records contain 2 double precision value*hours accumulators for each channel.
 * Currently the two are Volt*Hrs / hz.Hrs for VT channels and
 * Watt*Hrs / VA*Hrs for CT channels.
 * 
 * Given any two log records, the average volts, hz, watts or Irms for the period between them
 * can be determined, in addition to the basic metric like WattHrs.  Power factor (average) can 
 * be determined by dividing Watts/(Irms * Vrms) (Vrms is found in the CT channel's associated
 * VT channel bucket.
 * 
 * Entries are only made in real time when the CarbixEnergyMonitor is running, so they are not periodic,
 * but they are ordered.  It is relatively quick to find any record by key (UNIXtime) and a 
 * readKEY method is provided in the CarbixLog class.
 * 
 * As with all of the SERVICES, it has a  single function call and is implimented as state machine.
 * Services should try not to execute for more than a few milliseconds at a time.
 **********************************************************************************************/
 #include "CarbixEnergyMonitor.h"
 #define GapFill 600           // Fill in gaps of less than this seconds
 void dataLogWDT();
 void logtoHistory(CarbixLogRecord* logRecord);

 uint32_t dataLog(struct serviceBlock* _serviceBlock){
  enum states {initialize, synchronize, logData};
  static states state = initialize;                                                       
  static CarbixLogRecord* logRecord = new CarbixLogRecord;
  static double accum1Then [MAXINPUTS];
  static double accum2Then [MAXINPUTS];
  static uint32_t msThen = 0;
  static Ticker logWDT;

  switch(state){

    case initialize: {
      
            // If clock is not running, return

      if( ! RTCrunning || ! sampling) break;

      log("dataLog: service started.");

      // Initialize the CarbixLog class
      
      if(int rtc = Current_log.begin(CARBIX_CURRENT_LOG_PATH)){
        log("dataLog: Log file open failed. %d", rtc);
        dropDead();
      }

      // Initialize the CarbixLogRecord accums in case no context.

      for(int i=0; i<MAXINPUTS; i++){
        logRecord->accum1[i] = 0.0;
        logRecord->accum2[i] = 0.0;
      }

      // If it's a new log,
      // Check to see if there is a history log for context.
      
      if(Current_log.fileSize() == 0){
        log("dataLog: New current log created.");
        if(History_log.begin(CARBIX_HISTORY_LOG_PATH) == 0 && History_log.fileSize() > 0){
          logRecord->UNIXtime = History_log.lastKey();
          History_log.readKey(logRecord);
          log("dataLog: Last history entry: %s", datef(UTC2Local(logRecord->UNIXtime)).c_str());
        }
      }
      
      // If it's not a new log, get the last entry.

      else {
        logRecord->UNIXtime = Current_log.lastKey();
        Current_log.readKey(logRecord);
        log("dataLog: Last log entry %s", datef(UTC2Local(Current_log.lastKey())).c_str());
      }
 
        // If not at multiple of interval, return when we are.

      state = synchronize;
      if( ! UTCtime() % Current_log.interval()){
        return UTCtime() + Current_log.interval() - (UTCtime() % Current_log.interval());
      }
      
      // In sync, drop through.

    }

    case synchronize: {
      
      // Initialize local accumulators
      
      msThen = millis();
      for(int i=0; i<maxInputs; i++){
        CarbixInputChannel* _input = inputChannel[i];
        if(_input){
          inputChannel[i]->ageBuckets(msThen);
          accum1Then[i] = inputChannel[i]->dataBucket.accum1;
          accum2Then[i] = inputChannel[i]->dataBucket.accum2;
        }
      }

      // If it's been a long time since last entry, skip ahead.
      
      if((UTCtime() - logRecord->UNIXtime) > GapFill){
        logRecord->UNIXtime = UTCtime();
        logRecord->UNIXtime -= logRecord->UNIXtime % Current_log.interval();
      }

      // Set state to log on subsequent calls.

      state = logData;
      _serviceBlock->priority = priorityHigh;
      break;
    }
 
    case logData: {

      // If this seems premature.... get outta here.

      if(UTCtime() < logRecord->UNIXtime) return 2;

      // Save the old record if there are integration logs to update

      CarbixLogRecord *oldRecord = nullptr;
      if(integrations->count()){
        oldRecord = new CarbixLogRecord;
        memcpy(oldRecord, logRecord, sizeof(CarbixLogRecord));
        oldRecord->UNIXtime -= Current_log.interval();
      }

      // If log is up to date, update the entry with latest data.

      if(logRecord->UNIXtime >= UTCtime()){
        uint32_t msNow = millis();
        double elapsedHrs = double((uint32_t)(msNow - msThen)) / MS_PER_HOUR;
        for(int i=0; i<maxInputs; i++){
          CarbixInputChannel* _input = inputChannel[i];
          if(_input){
            _input->ageBuckets(msNow);
            logRecord->accum1[i] += _input->dataBucket.accum1 - accum1Then[i];
            if(logRecord->accum1[i] != logRecord->accum1[i]) logRecord->accum1[i] = 0;
            accum1Then[i] = _input->dataBucket.accum1;
            logRecord->accum2[i] += _input->dataBucket.accum2 - accum2Then[i];
            if(logRecord->accum2[i] != logRecord->accum2[i]) logRecord->accum2[i] = 0;
            accum2Then[i] = _input->dataBucket.accum2;
          }
          else {
            accum1Then[i] = 0;
            accum2Then[i] = 0;
          }
        }
        msThen = msNow;
        logRecord->logHours += elapsedHrs;
      }

      // Write the record
      
      Current_log.write(logRecord);

      // Courtesy call to History Log handler.
      // Will write appropriate records when synchronized.

      logtoHistory(logRecord);

      // If there are integrations,
      // Call their handlers to add new integration records.

      if(integrations->count()){
        Script *integration = integrations->first();
        while(integration){ 
          ((integrator*)integration->getParm())->newLogEntry(oldRecord, logRecord);
          integration = integration->next();
        }
        delete oldRecord;
      }

      // Logging data is the primary purpose of CarbixEnergyMonitor.
      // Set a WDT to make sure it continues.

      logWDT.detach();
      logWDT.attach(300, dataLogWDT);

      break;
    }
  }

  // Advance the time and return.
  
  logRecord->UNIXtime += Current_log.interval();
  return logRecord->UNIXtime;
}

/******************************************************************************
 * 
 *    The datalog WDT is set each time the datalog is updated. If it expires
 *    the datalog is not being updated.  The program may be stuck in a 
 *    loop somewhere.  Log a message and restart.  The trace will provide
 *    diagnostic information.
 * 
 *    Conditional on HTTPlock not set.  This is a proxy for update release
 *    download, which is the only place lock is currently used. During download,
 *    the update service retains control so this WDT could trigger if download
 *    is delayed.
 * 
 * *****************************************************************************/

void dataLogWDT(){
        if(! HTTPlock){
          log("dataLog: datalog WDT - restarting");
          ESP.restart();
        }
}
/******************************************************************************
 * logReadKey(carbixLogRecord) - read a keyed record from the combined log
 * 
 * This function brokers keyed log read requests, servicing them from the
 * appropriate log:
 * 
 * Current_log:
 * relatively recent data spanning the past 12 months.
 * small interval (5 seconds).
 * potentially slower access because it can have holes neccessitating searching.
 * 
 * History_log:
 * contains all of the data since the beginning of time.
 * large interval (60 seconds).
 * Look ma - no holes!  direct access w/o searching.
 * 
 * This function will decide the most appropriate log to retrieve the requested 
 * record.
 *  
 * ***************************************************************************/

uint32_t logReadKey(CarbixLogRecord* callerRecord) {
  uint32_t key = callerRecord->UNIXtime;

      // If history not open, 
      // use current

  if( ! History_log.isOpen()){
    return Current_log.readKey(callerRecord);
  }

      // If before current log, 
      // use history

  if(key < Current_log.firstKey()){
    return History_log.readKey(callerRecord);
  }

      // If not multiple of history interval,
      // use current

  if(key % History_log.interval()){
    return Current_log.readKey(callerRecord);
  }

      // If past end of history,
      // use current

  if(key > History_log.lastKey()){
    return Current_log.readKey(callerRecord);
  }

      // Use history

  return History_log.readKey(callerRecord);
}
